akita11/PETS_USBpower/USBconn.jpg

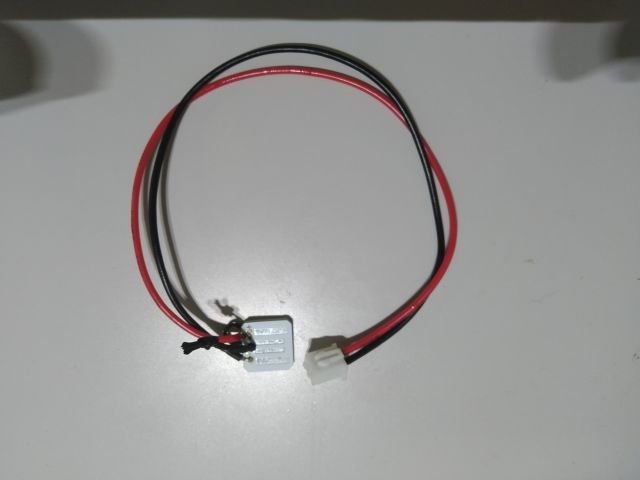
USBconn.jpg
