akita11/PETS_USBpower/instruction/org/2022-09-22 16.14.56.jpg

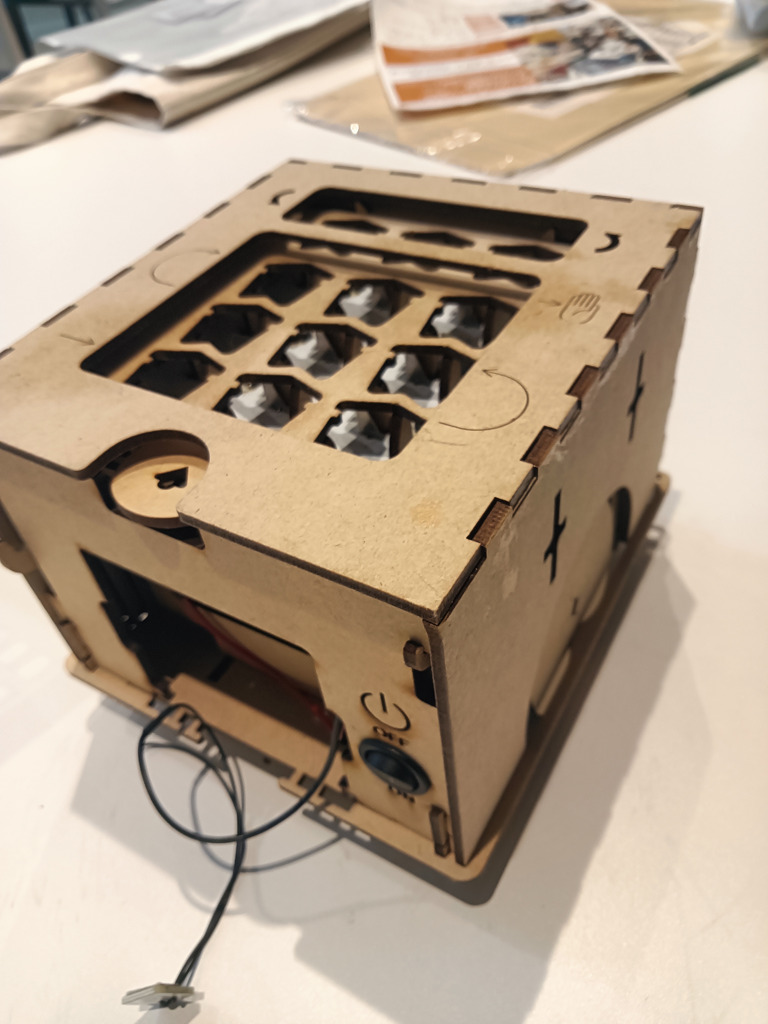
instruction/org/2022-09-22 16.14.56.jpg
